adityadabas1008/ANSreport/_manuscript/images/biquad_aslk_exp4.png

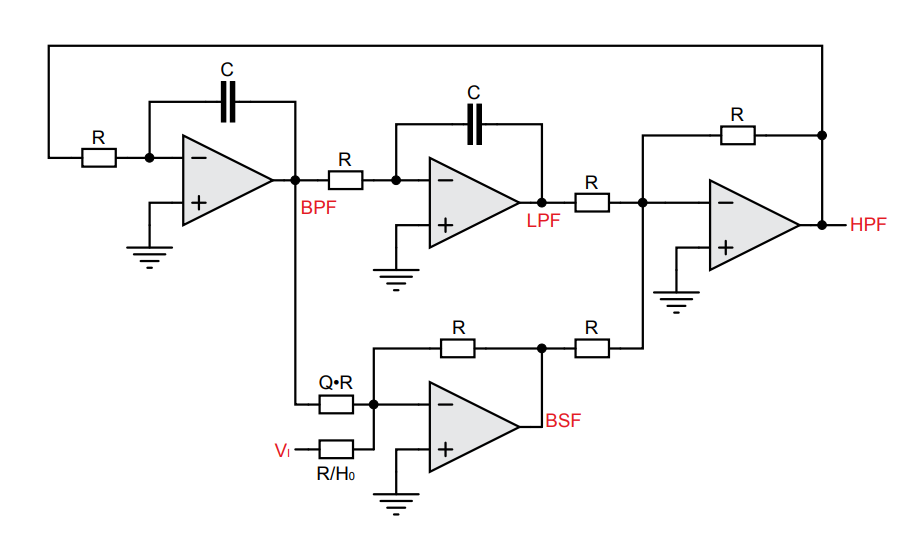
_manuscript/images/biquad_aslk_exp4.png
