adityadabas1008/ANSreport/_manuscript/images/butterworth.png

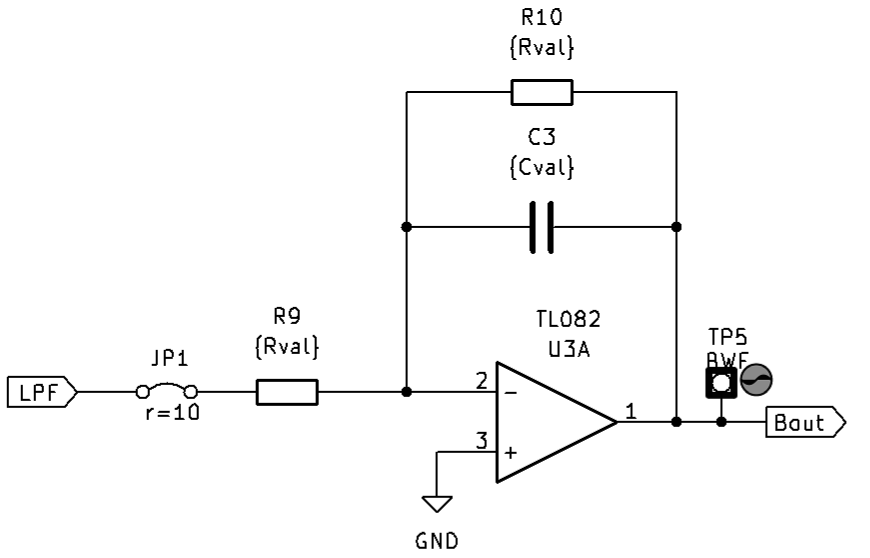
_manuscript/images/butterworth.png
