adityadabas1008/ANSreport/_manuscript/images/Güte_Faktor.png

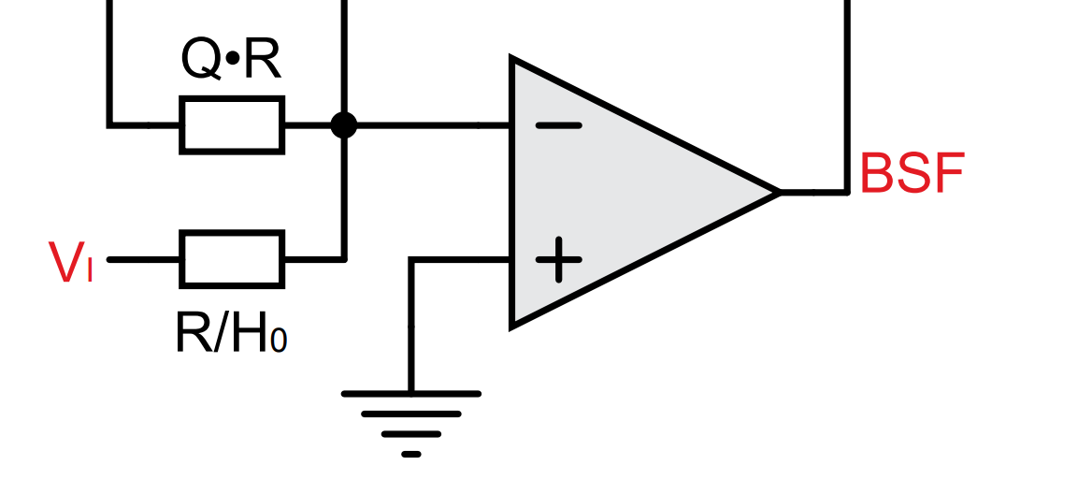
_manuscript/images/Güte_Faktor.png
