adityadabas1008/ANSreport/_manuscript/images/intopamp.png

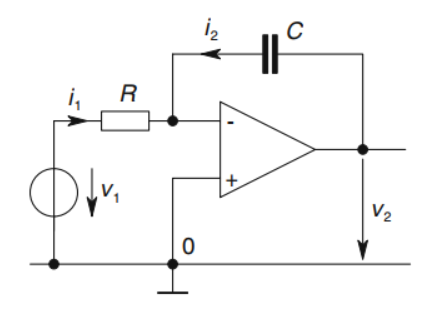
_manuscript/images/intopamp.png
