adityadabas1008/ANSreport/_manuscript/images/platine.jpg

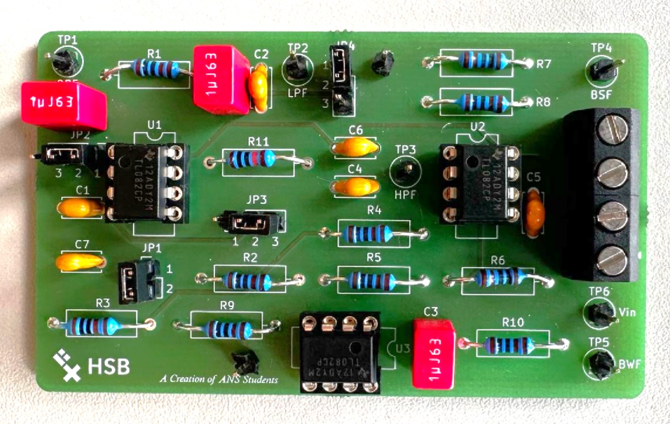
_manuscript/images/platine.jpg
