adityadabas1008/ANSreport/_manuscript/images/theorie_plot.png

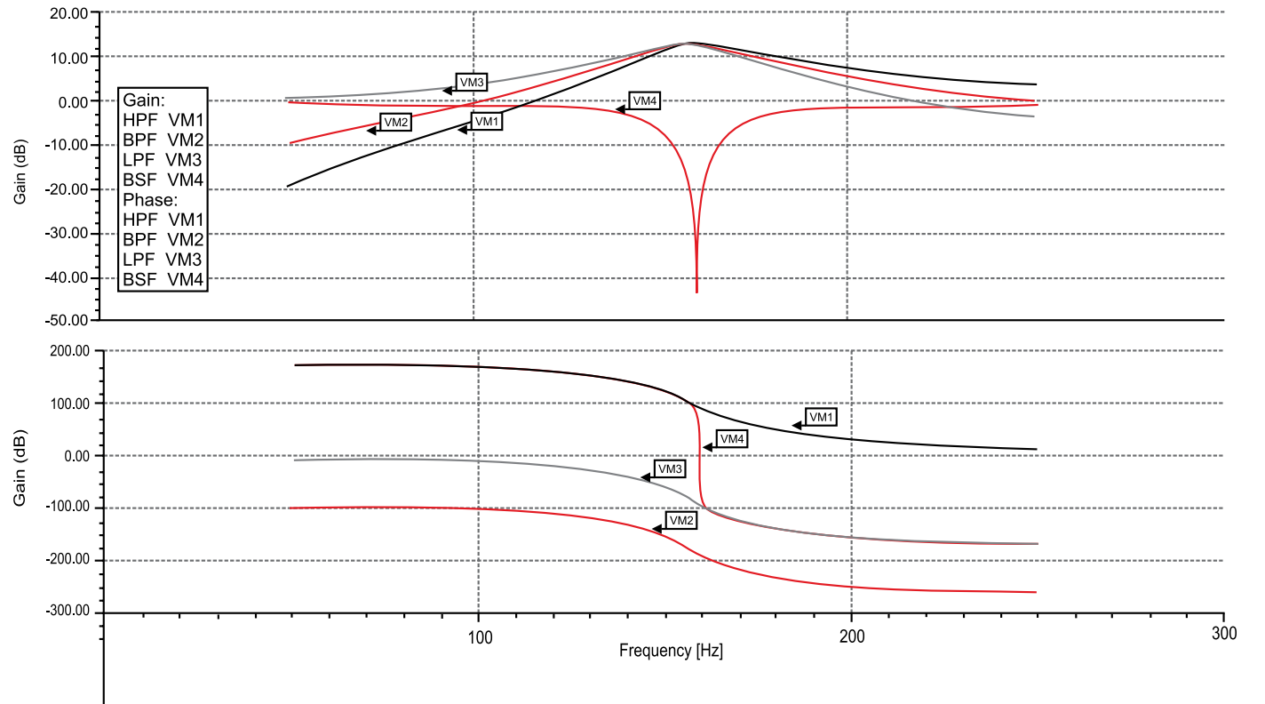
_manuscript/images/theorie_plot.png
