adityadabas1008/ANSreport/_manuscript/Mess_Sim_Vergleich/Q1/Bandstop_richtig_R6.png

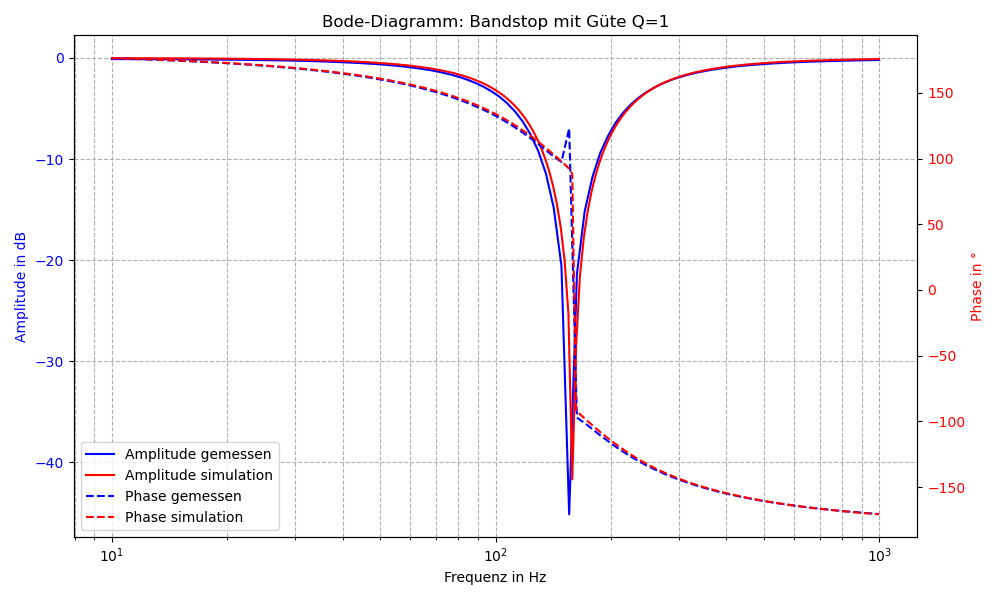
_manuscript/Mess_Sim_Vergleich/Q1/Bandstop_richtig_R6.png
