adityadabas1008/ANSreport/_manuscript/Mess_Sim_Vergleich/Q10/Bandpass_ohne_Dämpfung.png

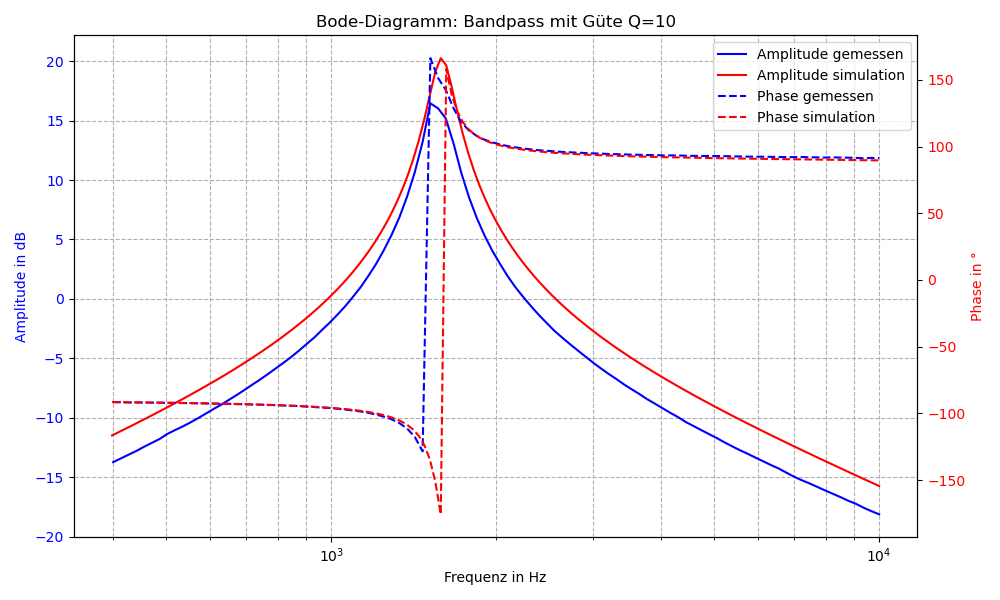
_manuscript/Mess_Sim_Vergleich/Q10/Bandpass_ohne_Dämpfung.png
