adityadabas1008/ANSreport/_manuscript/Mess_Sim_Vergleich/Q10/Hochpass_ohne_Dämpfung.png

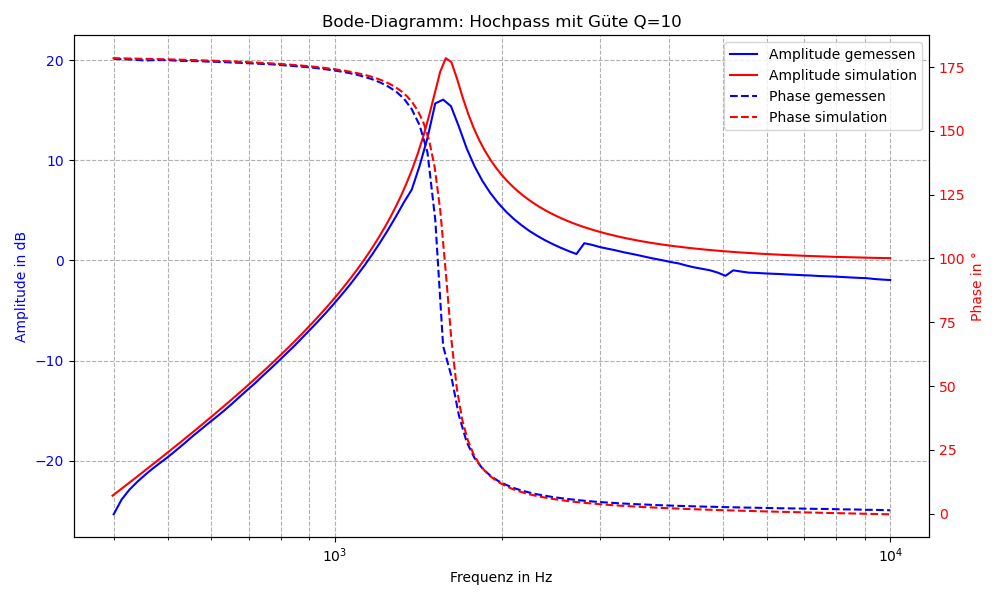
_manuscript/Mess_Sim_Vergleich/Q10/Hochpass_ohne_Dämpfung.png
