adityadabas1008/ANSreport/_manuscript/Mess_Sim_Vergleich/Q10/Tiefpass.png

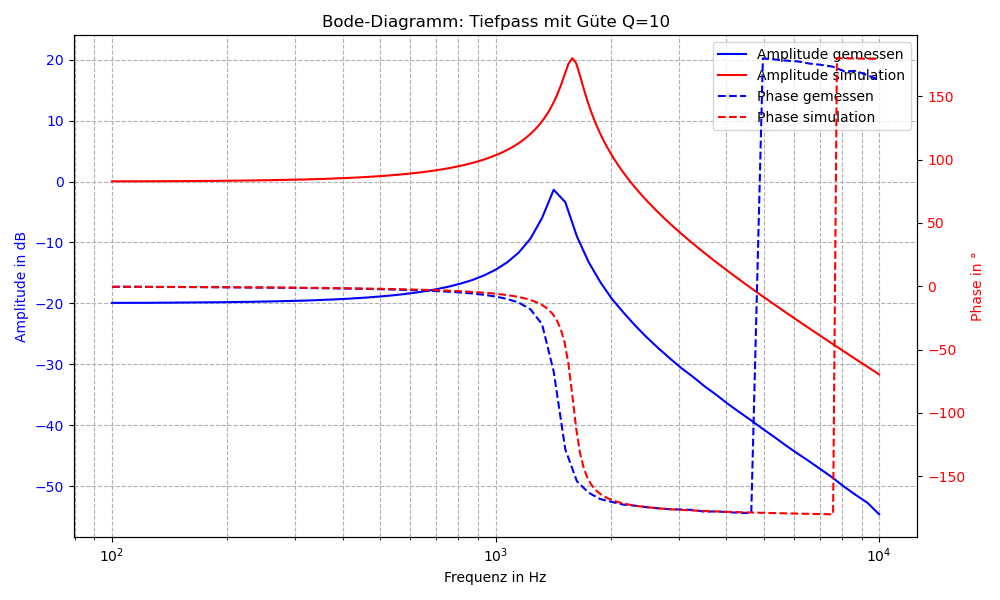
_manuscript/Mess_Sim_Vergleich/Q10/Tiefpass.png
