adityadabas1008/ANSreport/_manuscript/platine_sim_vergleich/Butter_platine_sim.png

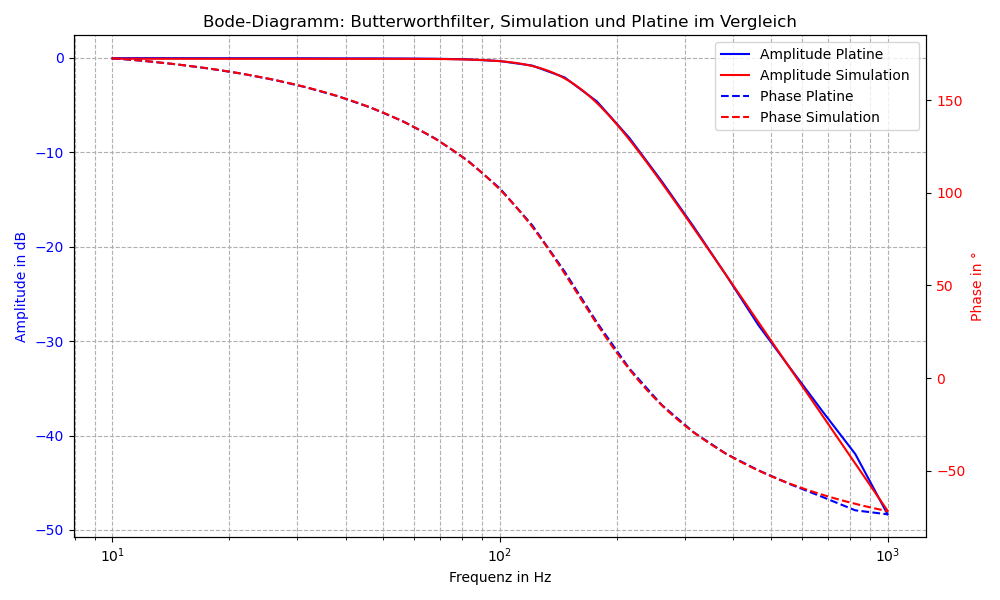
_manuscript/platine_sim_vergleich/Butter_platine_sim.png
