adityadabas1008/ANSreport/_manuscript/platine_sim_vergleich/Q1/Bandstop.png

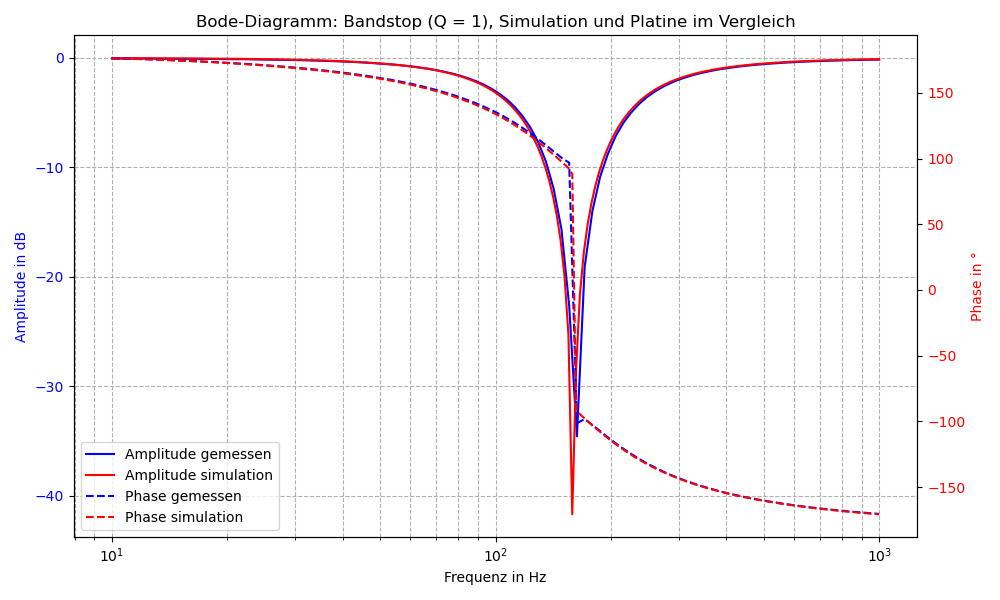
_manuscript/platine_sim_vergleich/Q1/Bandstop.png
