adityadabas1008/ANSreport/_manuscript/platine_sim_vergleich/Q1/Hochpass.png

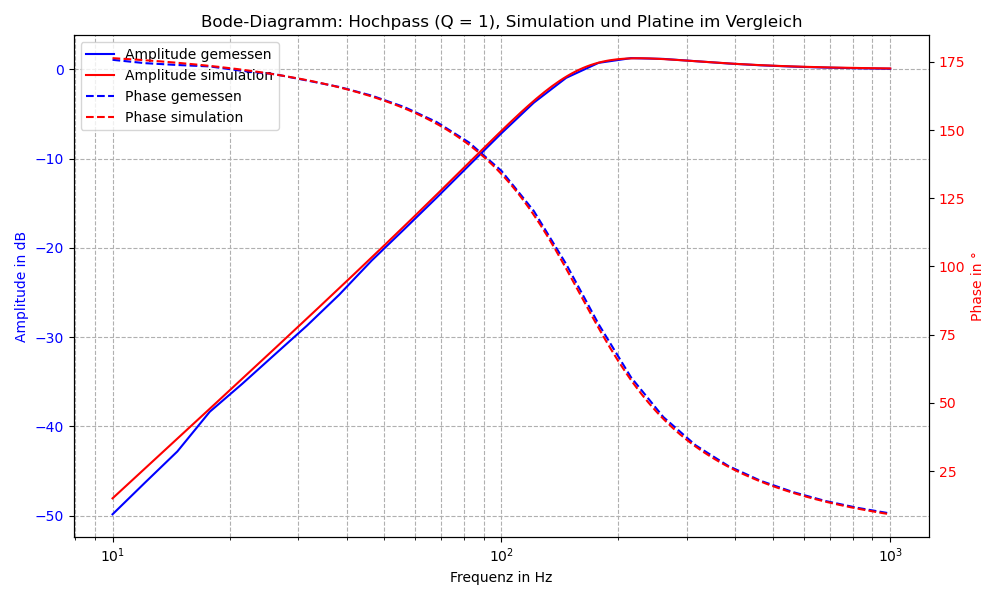
_manuscript/platine_sim_vergleich/Q1/Hochpass.png
