adityadabas1008/ANSreport/_manuscript/platine_sim_vergleich/Q10/Bandpass.png

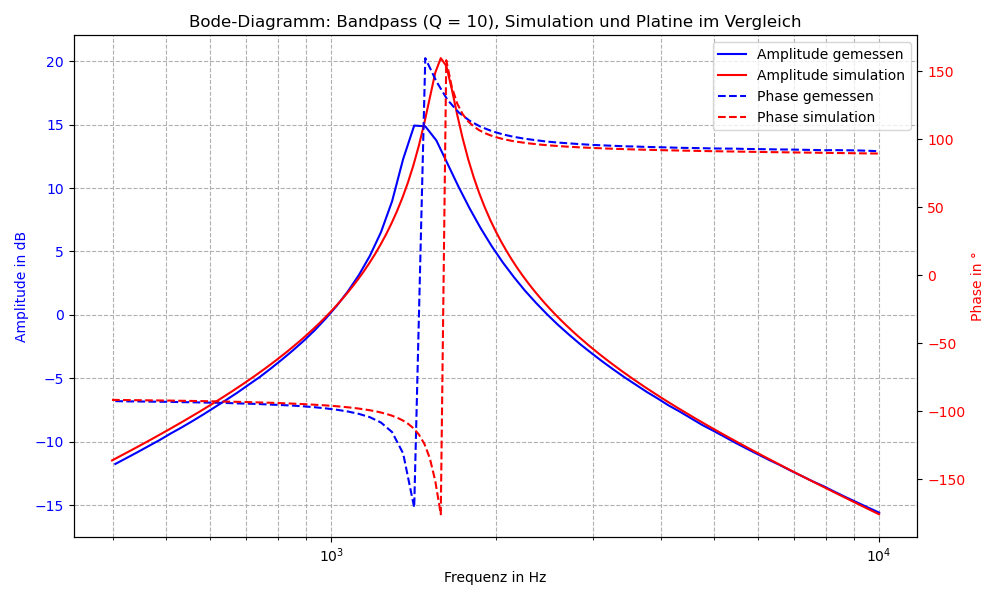
_manuscript/platine_sim_vergleich/Q10/Bandpass.png
