adityadabas1008/ANSreport/_manuscript/platine_sim_vergleich/Q10/Bandstop.png

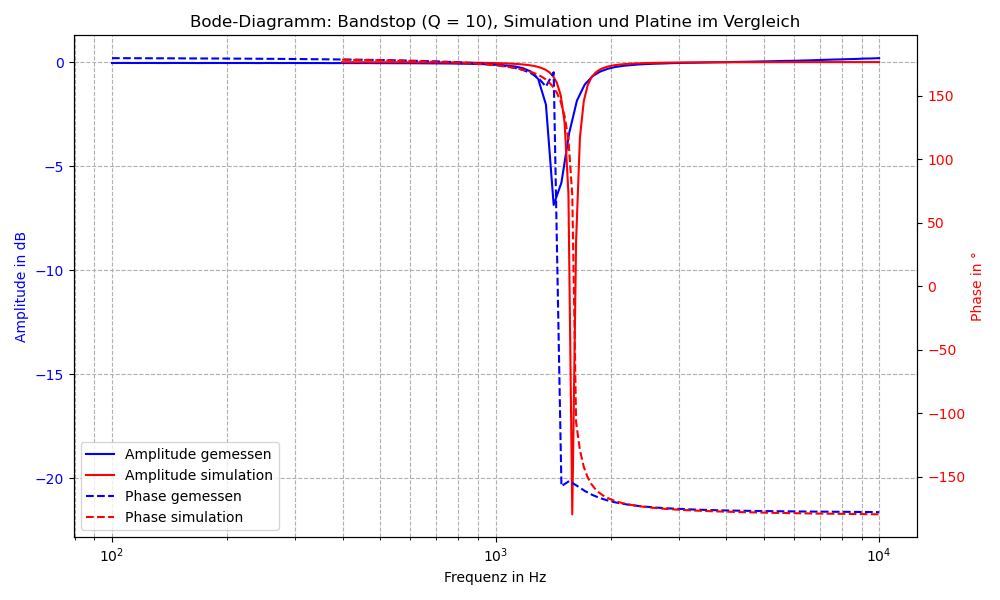
_manuscript/platine_sim_vergleich/Q10/Bandstop.png
