adityadabas1008/ANSreport/_manuscript/simulation/Butter_Tiefpass_Sim_Plot.png

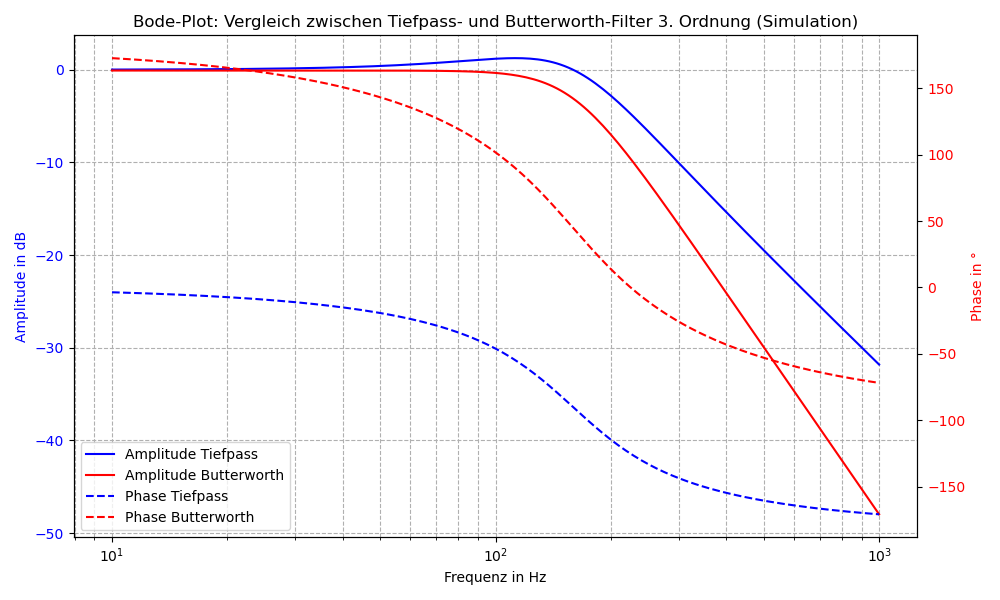
_manuscript/simulation/Butter_Tiefpass_Sim_Plot.png
