adityadabas1008/ANSreport/_manuscript/simulation/Q1_Plot.png

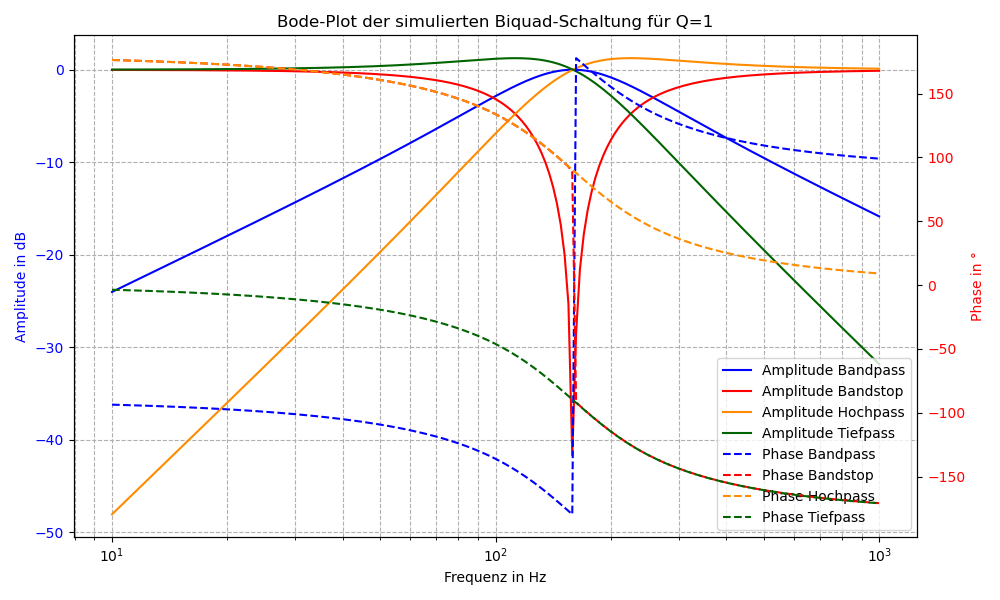
_manuscript/simulation/Q1_Plot.png
