adityadabas1008/ANSreport/_manuscript/simulation/Q10_Plot.png

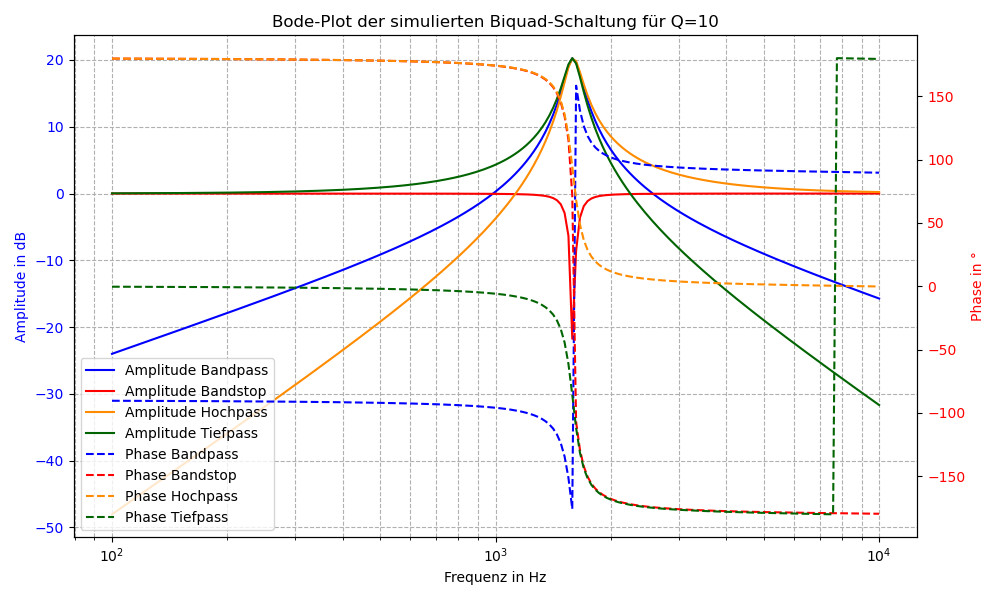
_manuscript/simulation/Q10_Plot.png
