adityadabas1008/ANSreport/Bode_Analyser/Butter/graphs.jpg

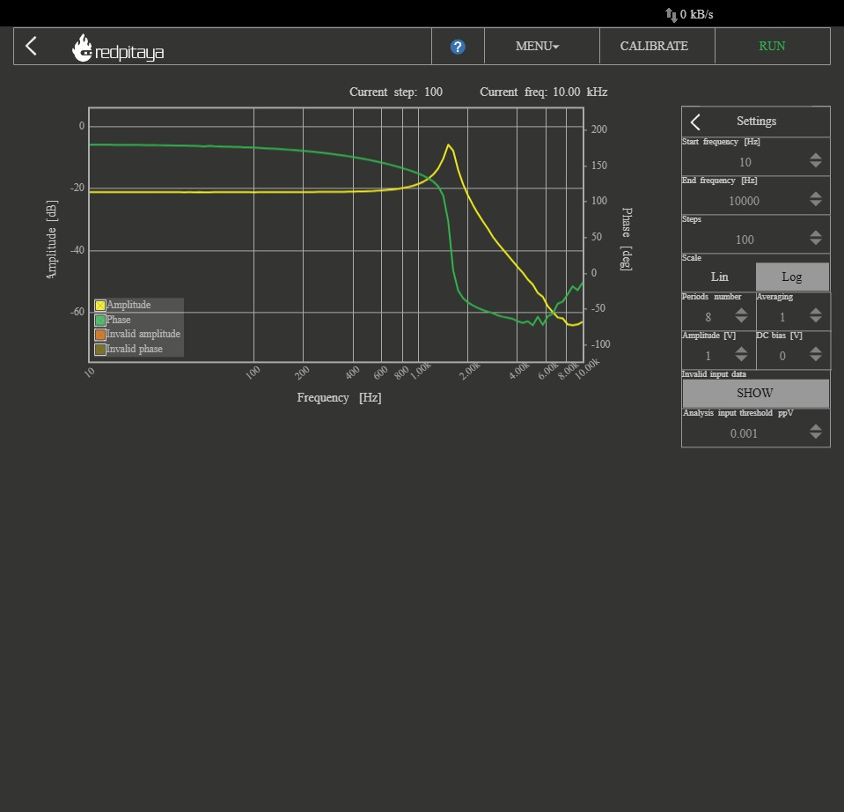
Bode_Analyser/Butter/graphs.jpg
