adityadabas1008/ANSreport/Bode_Analyser/Figure 2025-05-13 123255.png

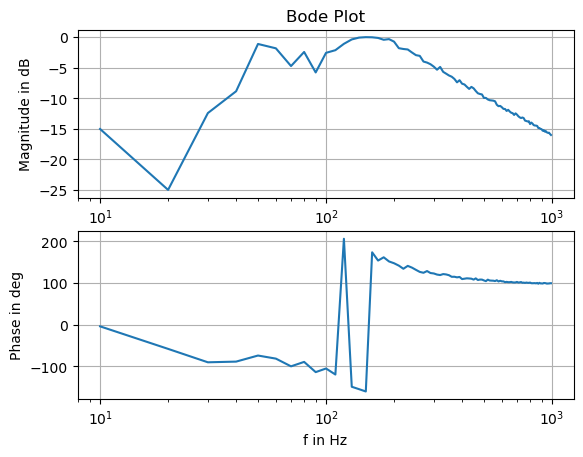
Bode_Analyser/Figure 2025-05-13 123255.png
