adityadabas1008/ANSreport/Bode_Analyser/Q1/Bandstop/neue_messung2/graphs.jpg

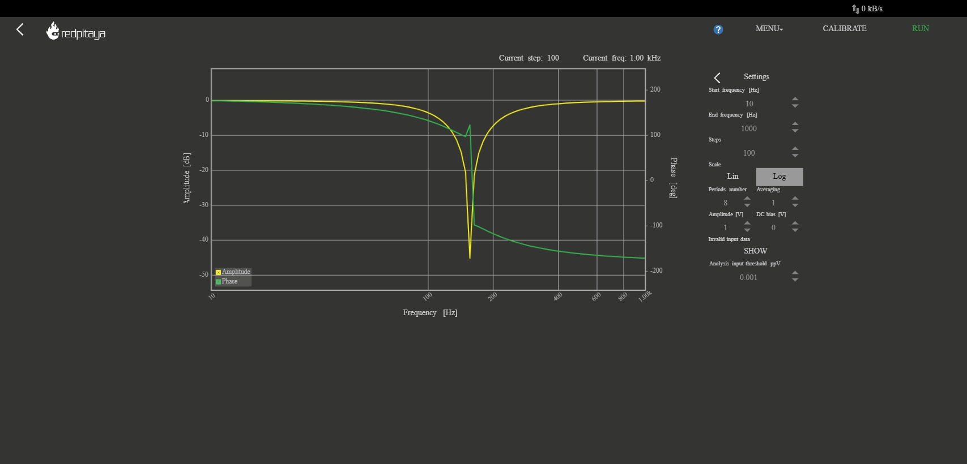
Bode_Analyser/Q1/Bandstop/neue_messung2/graphs.jpg
