adityadabas1008/ANSreport/Bode_Analyser/Q1/Bandstop/Plot_BS.png

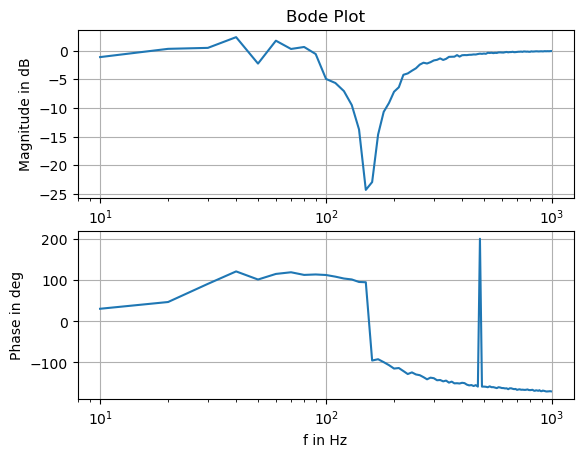
Bode_Analyser/Q1/Bandstop/Plot_BS.png
