adityadabas1008/ANSreport/Bode_Analyser/Q1/Highpass/Plot_HP.png

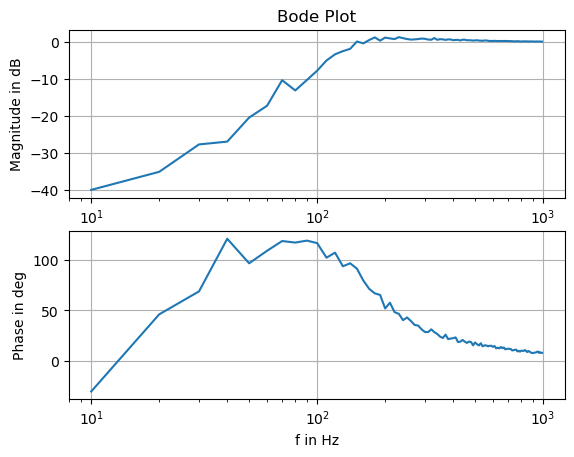
Bode_Analyser/Q1/Highpass/Plot_HP.png
