adityadabas1008/ANSreport/Bode_Analyser/Q1/Lowpass/Plot_TP.png

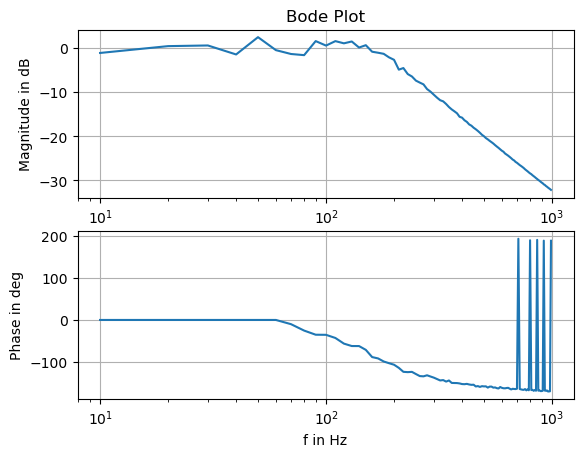
Bode_Analyser/Q1/Lowpass/Plot_TP.png
