adityadabas1008/ANSreport/Bode_Analyser/Q10/4_3_square/bandsperre.jpg

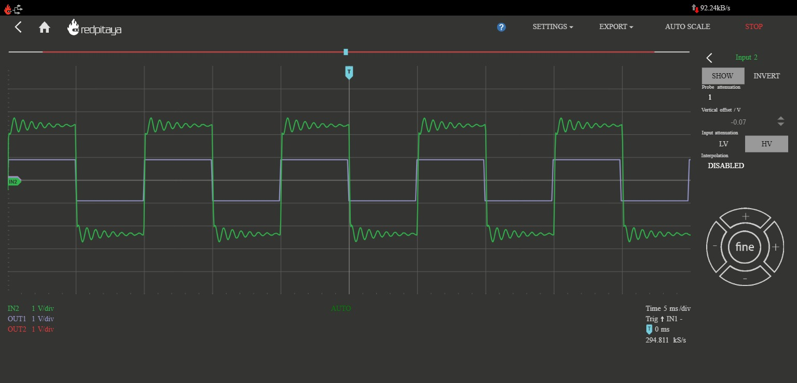
Bode_Analyser/Q10/4_3_square/bandsperre.jpg
