adityadabas1008/ANSreport/Bode_Analyser/Q10/4_3_square/graphs_Bandpass (2).jpg

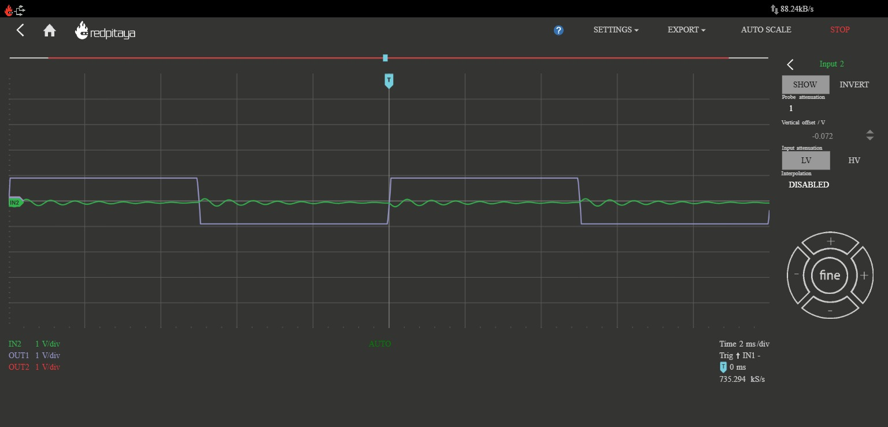
Bode_Analyser/Q10/4_3_square/graphs_Bandpass (2).jpg
