adityadabas1008/ANSreport/Bode_Analyser/Q10/Bandpass/Figure_2.png

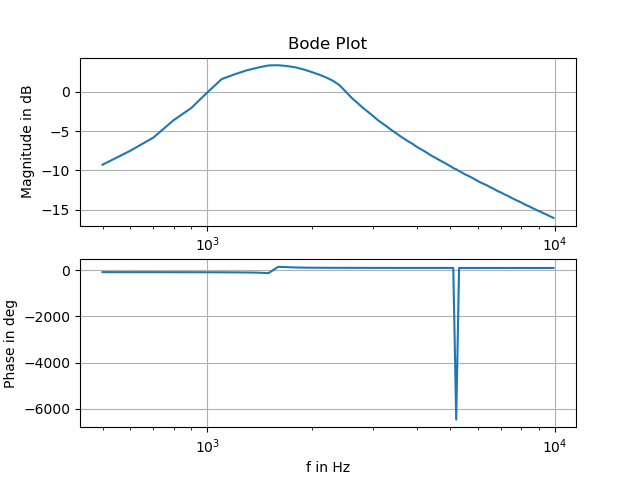
Bode_Analyser/Q10/Bandpass/Figure_2.png
