adityadabas1008/ANSreport/Bode_Analyser/Q10/Bandstop/Figure_2.png

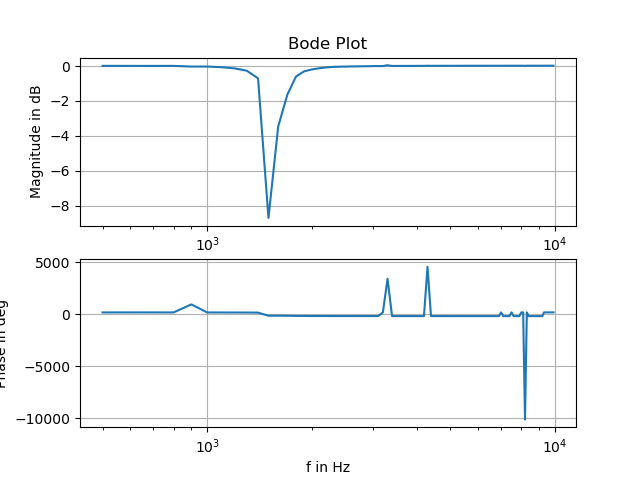
Bode_Analyser/Q10/Bandstop/Figure_2.png
