adityadabas1008/ANSreport/Bode_Analyser/Q10/Bandstop/neue_messung/graphs.jpg

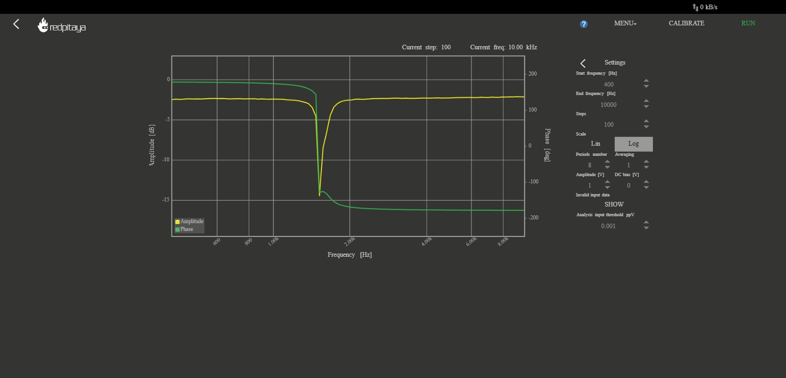
Bode_Analyser/Q10/Bandstop/neue_messung/graphs.jpg
