adityadabas1008/ANSreport/Bode_Analyser/Q10/Hochpass/Figure_2.png

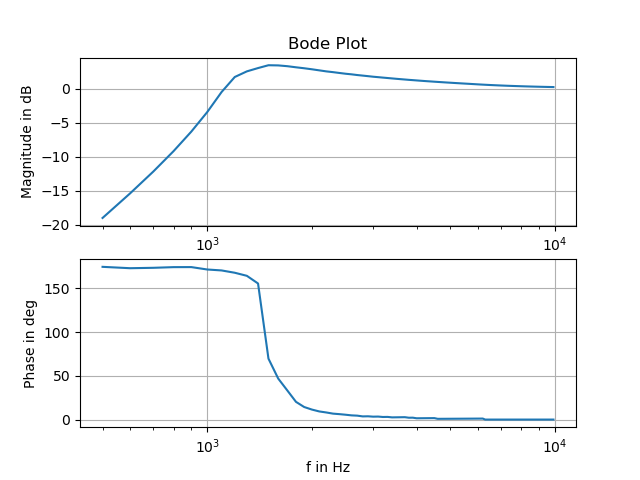
Bode_Analyser/Q10/Hochpass/Figure_2.png
