adityadabas1008/ANSreport/Bode_Analyser/Q10/Hochpass/neue_messung/graphs.jpg

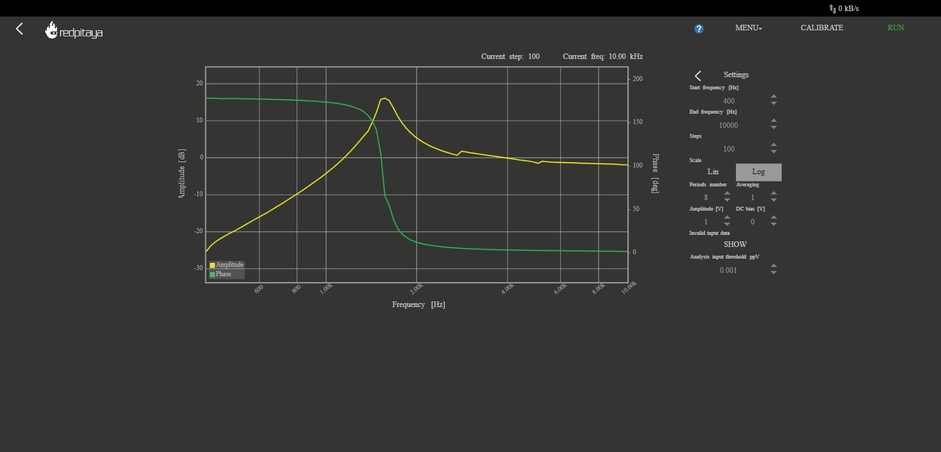
Bode_Analyser/Q10/Hochpass/neue_messung/graphs.jpg
