adityadabas1008/ANSreport/Bode_Analyser/Q10/Tiefpass/Figure_2.png

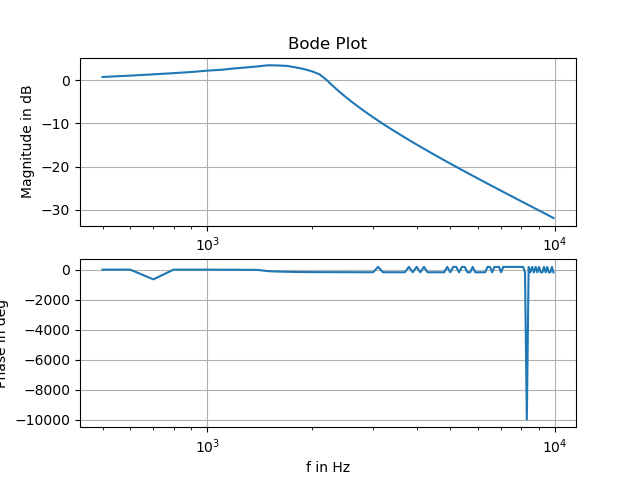
Bode_Analyser/Q10/Tiefpass/Figure_2.png
