adityadabas1008/ANSreport/Bode_Analyser/Q10/Tiefpass/neue_messung/graphs.jpg

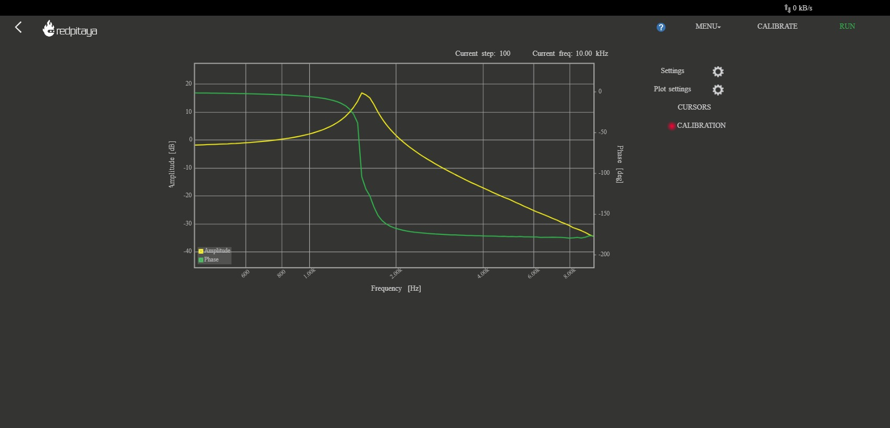
Bode_Analyser/Q10/Tiefpass/neue_messung/graphs.jpg
