adityadabas1008/ANSreport/images/Bodeplot_Q1.png

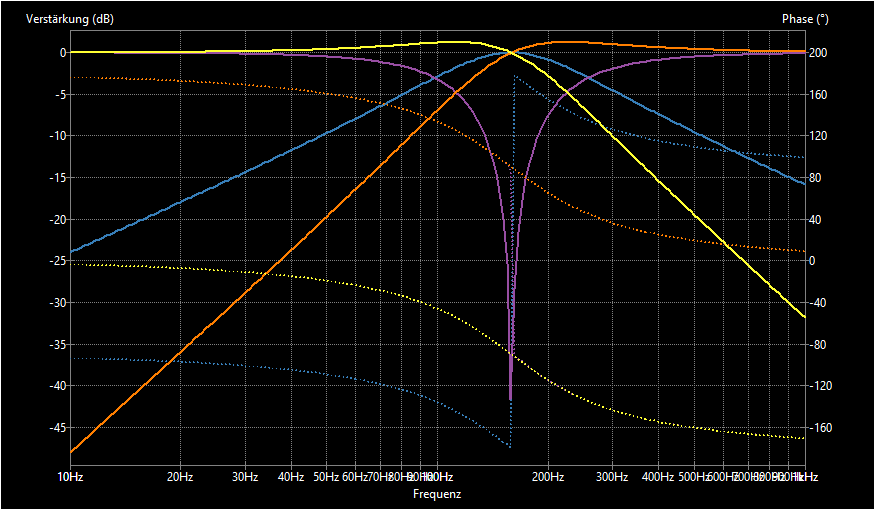
images/Bodeplot_Q1.png
