adityadabas1008/ANSreport/images/Bodeplot_Q10.png

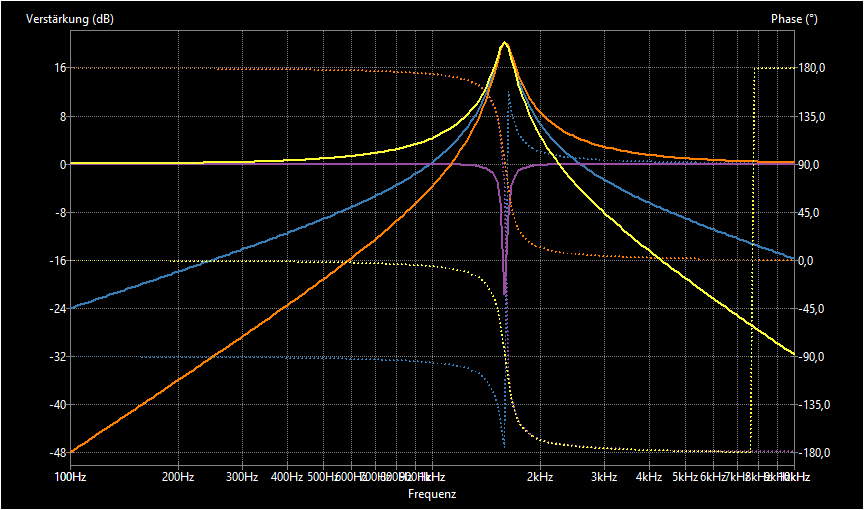
images/Bodeplot_Q10.png
