adityadabas1008/ANSreport/images/Kicad_Schaltung.png

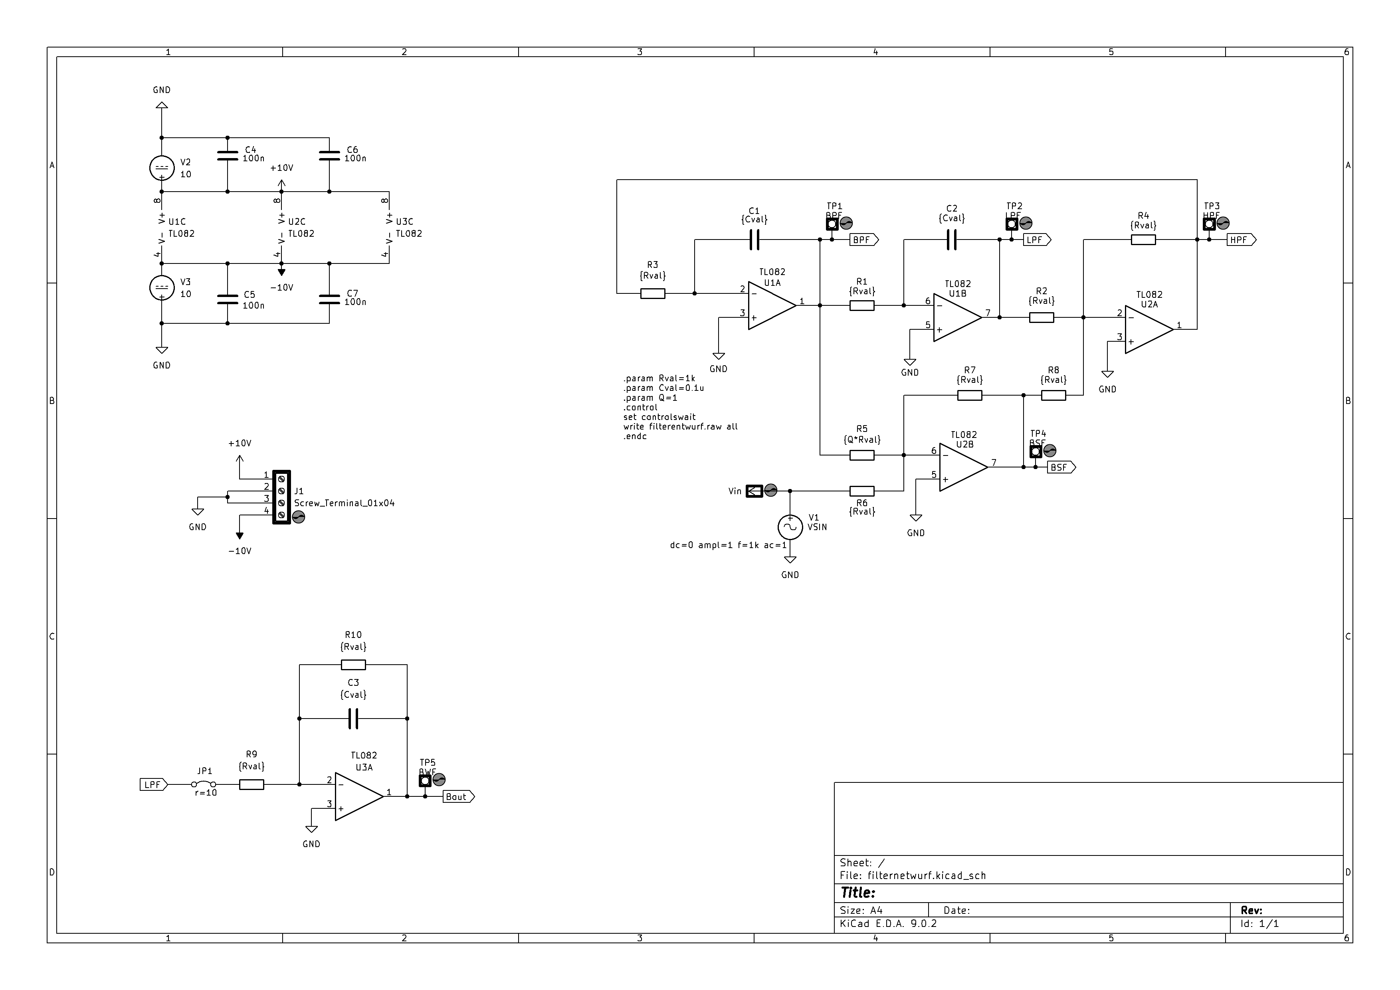
images/Kicad_Schaltung.png
