adityadabas1008/ANSreport/platine_messungen/Butter/graphs.jpg

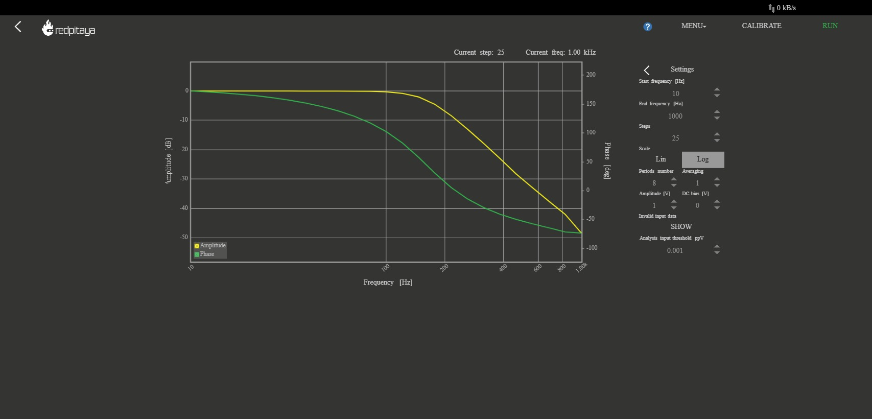
platine_messungen/Butter/graphs.jpg
