adityadabas1008/ANSreport/platine_messungen/Q1/Bandpass/graphs.jpg

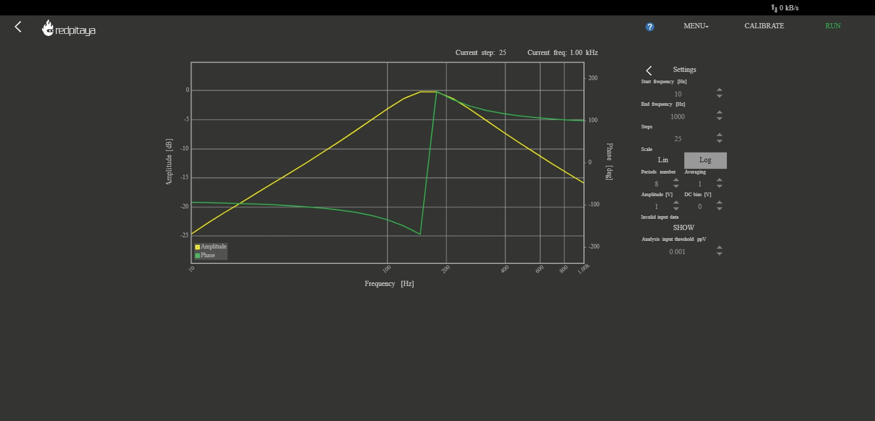
platine_messungen/Q1/Bandpass/graphs.jpg
