adityadabas1008/ANSreport/platine_messungen/Q1/Hochpass/graphs.jpg

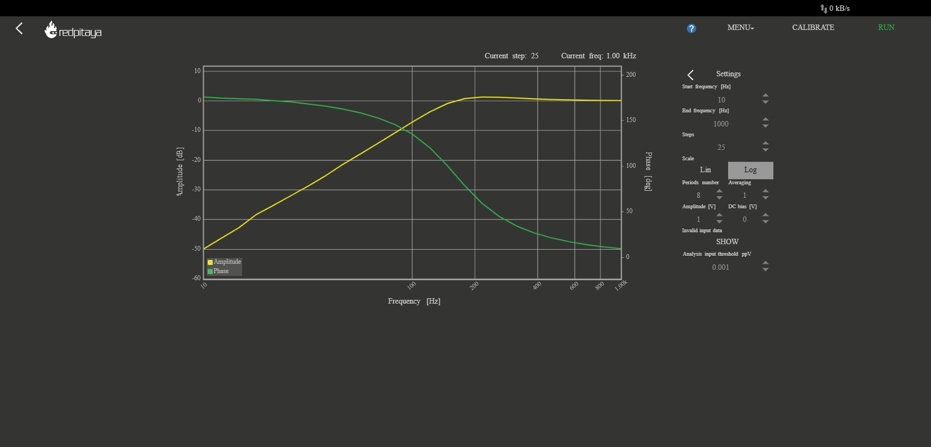
platine_messungen/Q1/Hochpass/graphs.jpg
