adityadabas1008/ANSreport/platine_messungen/Q1/Tiefpass/graphs.jpg

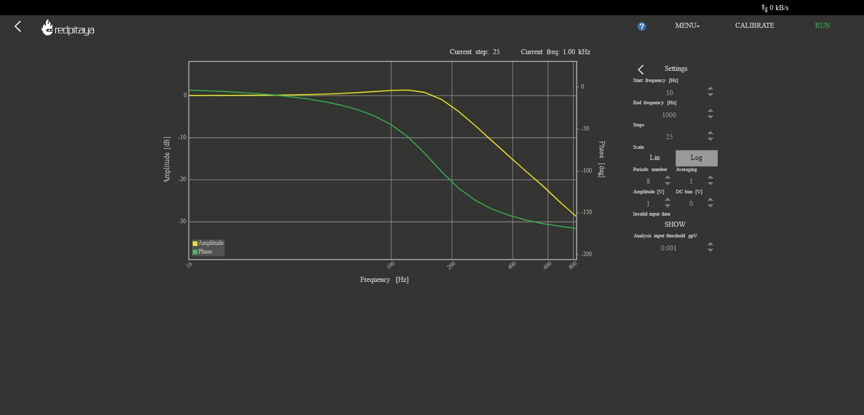
platine_messungen/Q1/Tiefpass/graphs.jpg
