adityadabas1008/ANSreport/platine_messungen/Q10/Bandpass/graphs.jpg

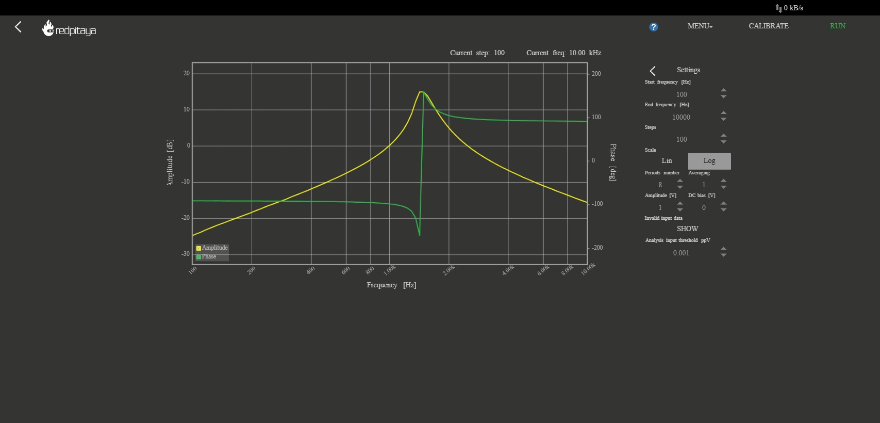
platine_messungen/Q10/Bandpass/graphs.jpg
