adityadabas1008/ANSreport/platine_messungen/Q10/Tiefpass/graphs.jpg

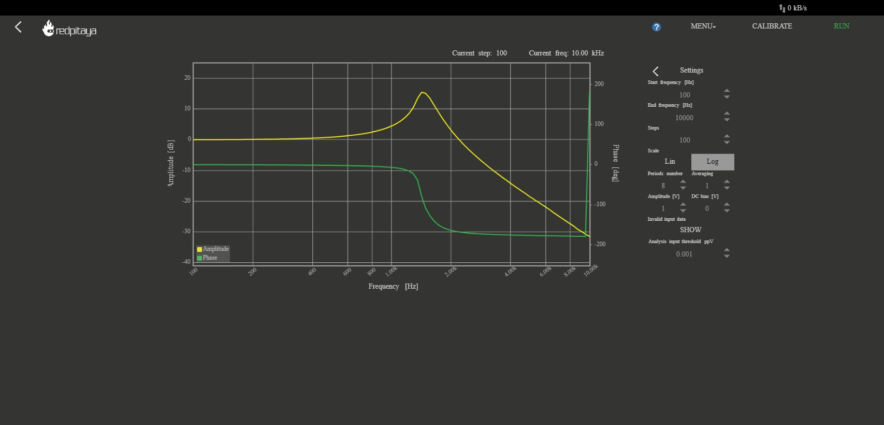
platine_messungen/Q10/Tiefpass/graphs.jpg
