adityadabas1008/ANSreport/Platine_sim_vergleich/Butter_vs_Tiefpass_platine.png

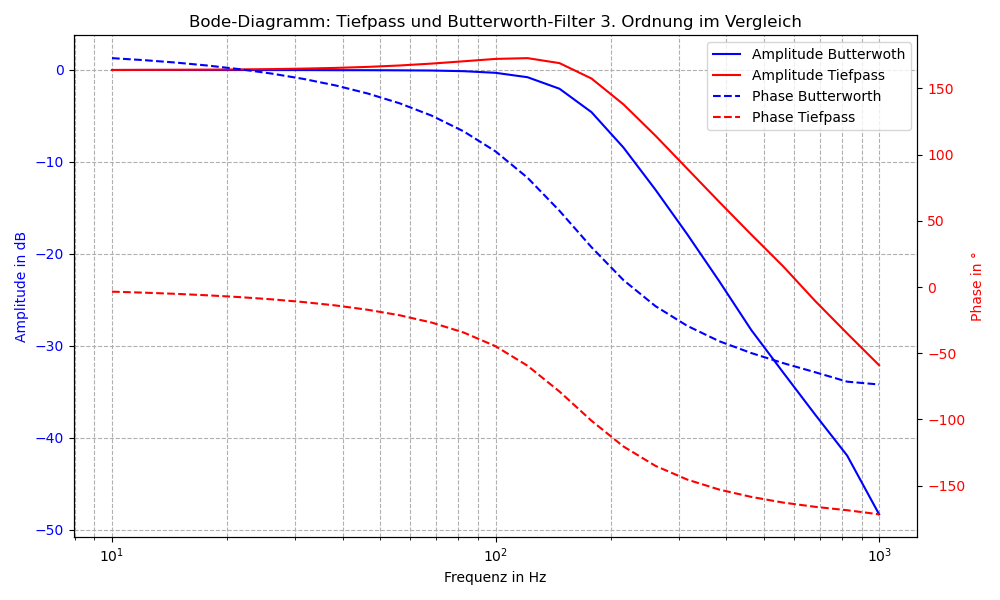
Platine_sim_vergleich/Butter_vs_Tiefpass_platine.png
